sjgray/MicroUK101/Grant's Files/MicroUK101-original circuit.jpg

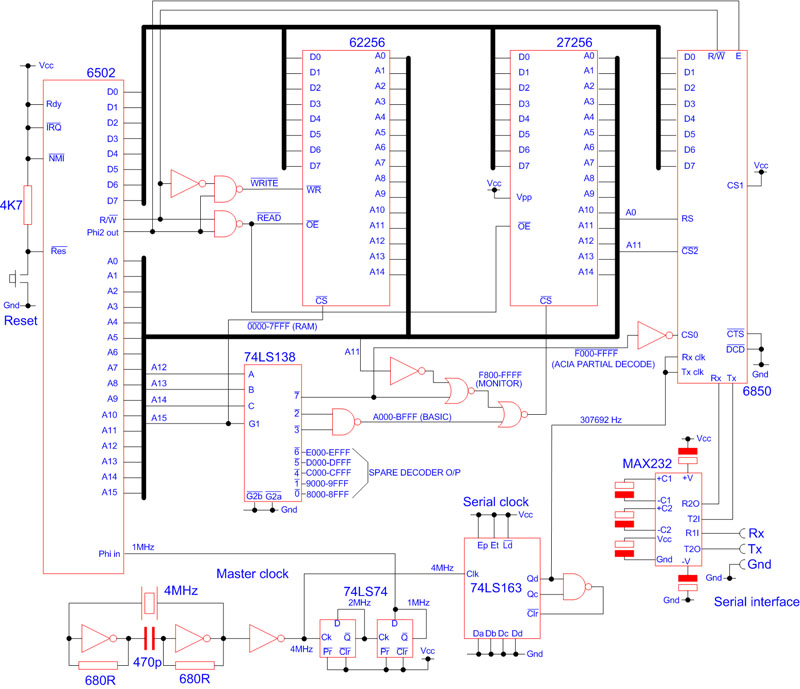
Grant's Files/MicroUK101-original circuit.jpg
