sjgray/MicroUK101/Pics/MicroUK101-pcb-2016-05-26.png

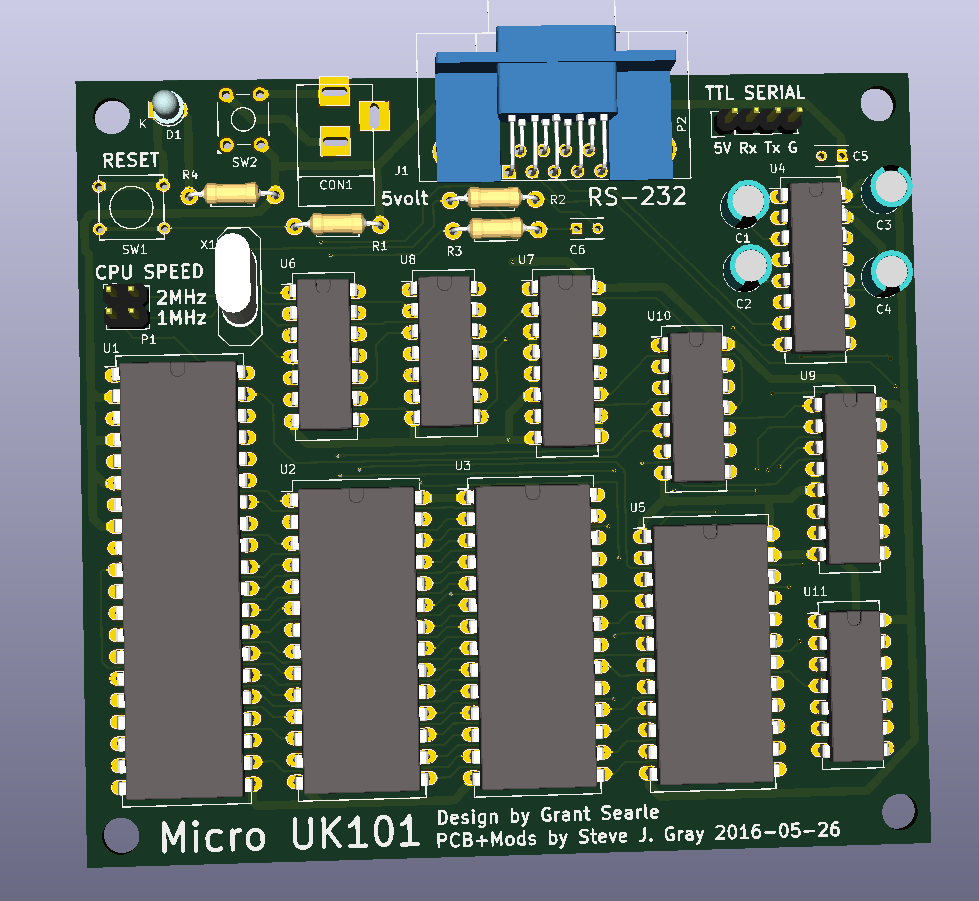
Pics/MicroUK101-pcb-2016-05-26.png
