sjgray/MicroUK101/Pics/MicroUK101-pcb-2016-09-05.png

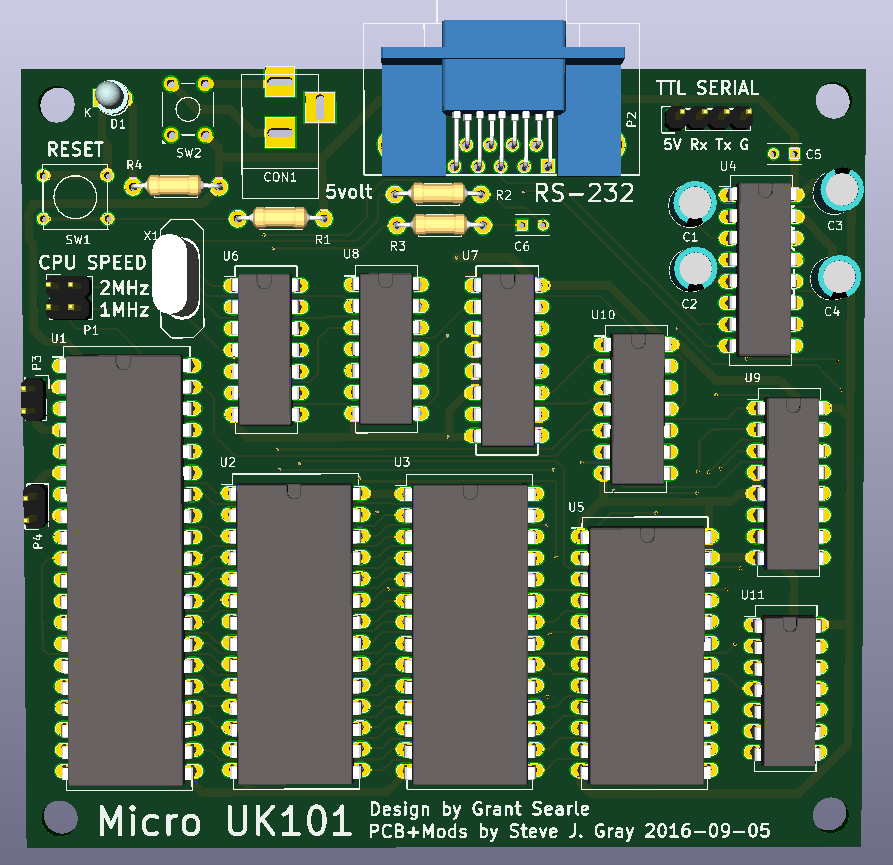
Pics/MicroUK101-pcb-2016-09-05.png
